kred/EBSHackathon/Firmware/images/einstein.bmp

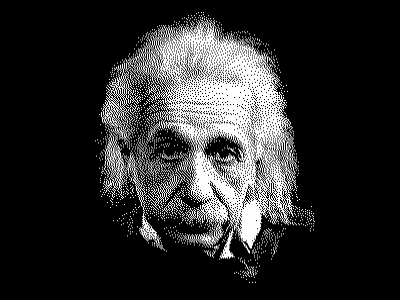
Firmware/images/einstein.bmp
