kred/EBSHackathon/Firmware/images/sklodowska.bmp

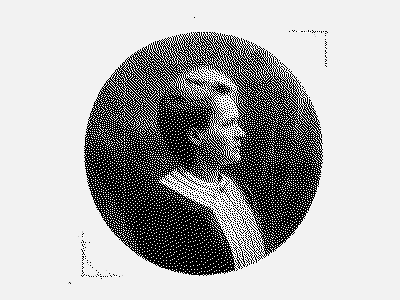
Firmware/images/sklodowska.bmp
